UtkarshVerma/ESPer/Edited Pictures/Drilled -Top View.jpg

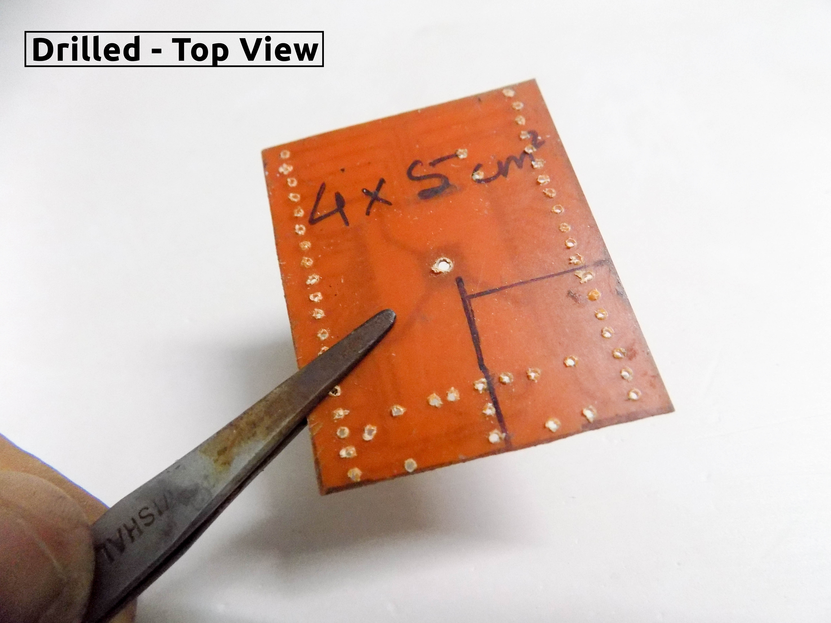
Edited Pictures/Drilled -Top View.jpg
